liubo817/Diplomna-Rabota/Mechanical details/SmallBox.stl

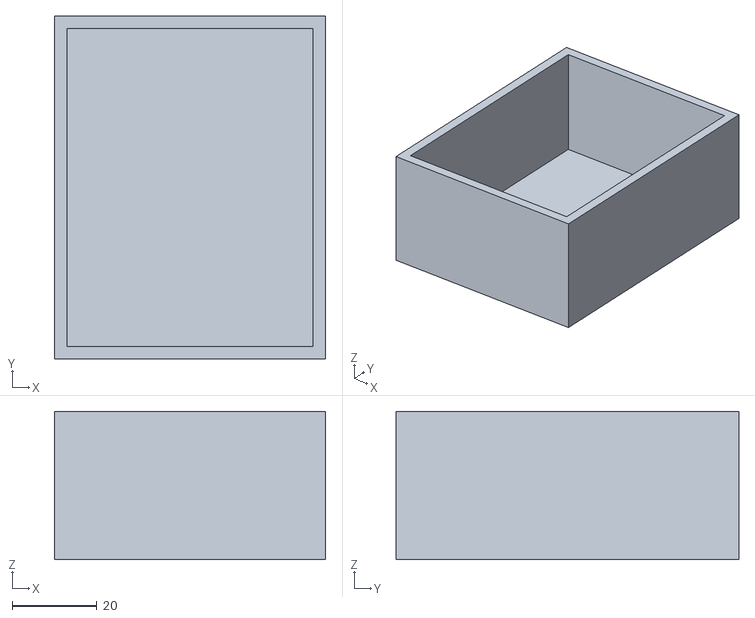
[picture p17: CAD file, 2024-02-20]
Mechanical details/SmallBox.stl
64.0 x 81.0 x 35.0
