liubo817/Diplomna-Rabota/Hardware/Libraries and 3D models/3p_con/connector_3p v1.step

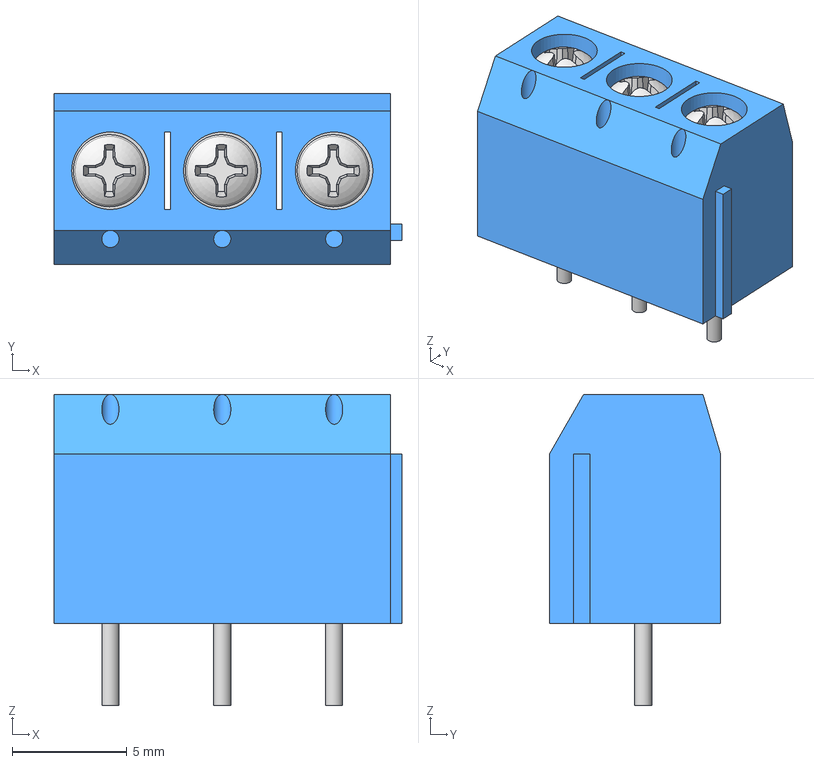
[picture p18: CAD file, 2024-01-03, an earlier design]
Hardware/Libraries and 3D models/3p_con/connector_3p v1.step
15.2 x 7.48 x 13.6 mm
