liubo817/Diplomna-Rabota/Hardware/Boards/FullBoard_V2/FullBoard.kicad_sch

## KiCad design Hardware/Boards/FullBoard_V2/FullBoard.kicad_sch (2024-01-07)

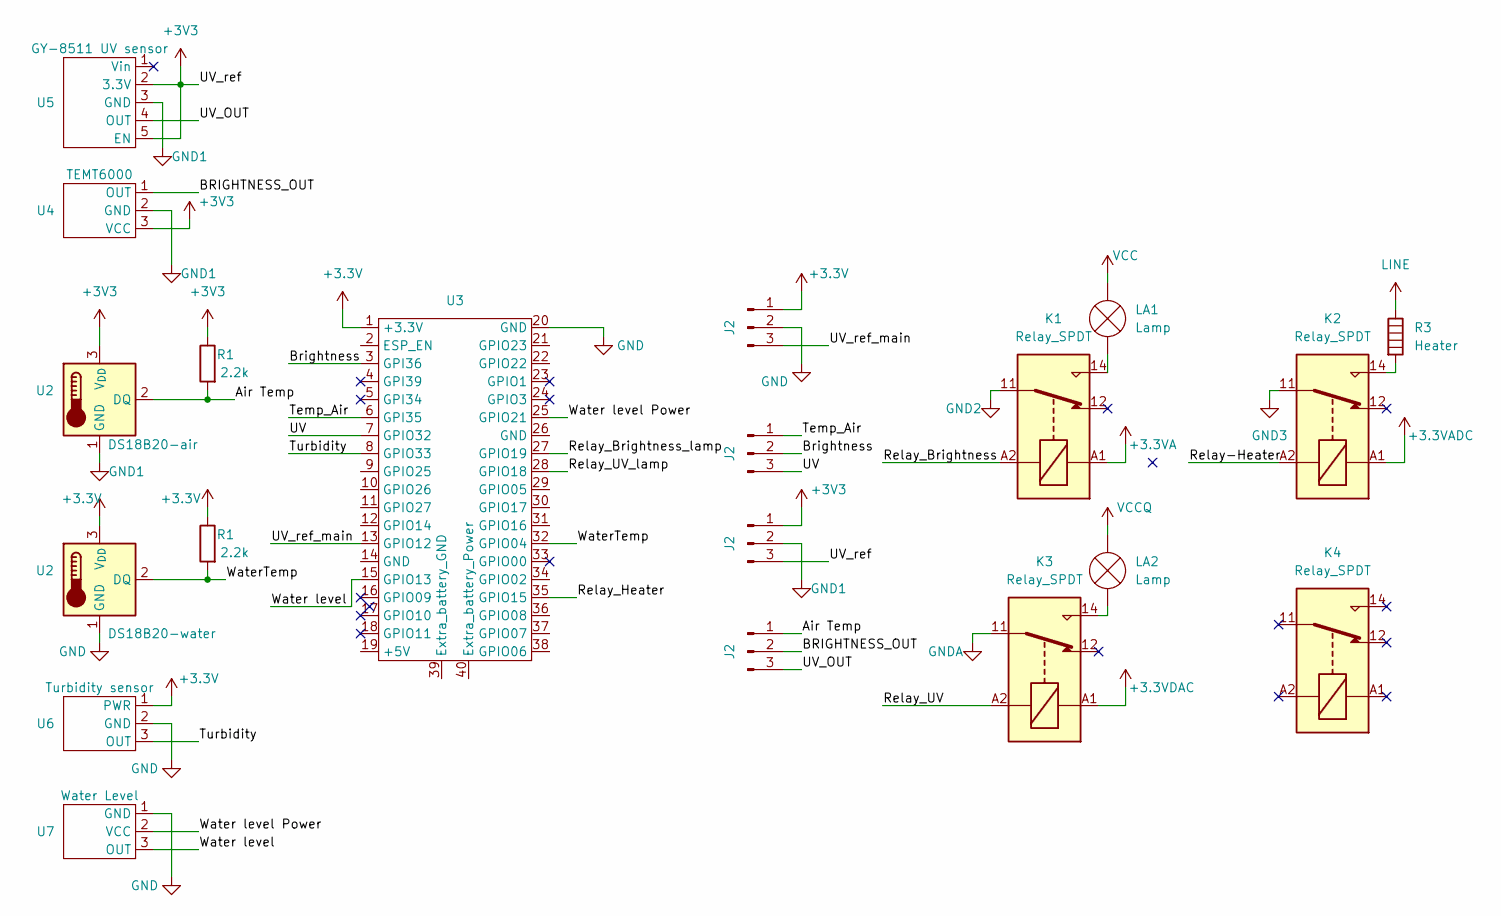
[picture p27: schematic FullBoard.kicad_sch]

Parts:
J2: Conn_01x03_Pin; connector_3p
K1, K2, K3: Relay_SPDT; Relay
K4: Relay_SPDT
LA1, LA2: Lamp
R1: 2.2k; R_Axial_DIN0204_L3.6mm_D1.6mm_P7.62mm_Horizontal
R3: Heater
U2: DS18B20-water; DS18B20_3dmodel
U3: MODULE_ESP32-DEVKITC
U4: TEMT6000; 3pin_holes
U5: GY-8511 UV sensor; 5pin_holes
U6: Turbidity sensor; 3pin_holes
U7: Water Level; 3pin_holes

Connections:
+3.3V: J2.1, R1.1, U2.3 (V_{DD}), U3.1 (+3.3V), U6.1 (PWR)
+3.3VA: K1.A1
+3.3VADC: K2.A1
+3.3VDAC: K3.A1
+3V3: J2.1, J2.3, R1.1, U2.3 (V_{DD}), U4.3 (VCC), U5.2 (3.3V), U5.5 (EN)
Air Temp: J2.1, R1.2, U2.2 (DQ)
BRIGHTNESS_OUT: J2.2, U4.1 (OUT)
Brightness: J2.2, U3.3 (GPI36)
GND: J2.2, U2.1 (GND), U3.20 (GND), U6.2 (GND), U7.1 (GND)
GND1: J2.2, U2.1 (GND), U4.2 (GND), U5.3 (GND)
GND2: K1.11
GND3: K2.11
GNDA: K3.11
LINE: R3.1
unnamed: K1.14, LA1.1 (-)
unnamed: K2.14, R3.2
unnamed: K3.14, LA2.1 (-)
Relay-Heater: K2.A2
Relay_Brightness: K1.A2
Relay_Brightness_lamp: U3.27 (GPIO19)
Relay_Heater: U3.35 (GPIO15)
Relay_UV: K3.A2
Relay_UV_lamp: U3.28 (GPIO18)
Temp_Air: J2.1, U3.6 (GPI35)
Turbidity: U3.8 (GPIO33), U6.3 (OUT)
UV: J2.3, U3.7 (GPIO32)
UV_OUT: J2.3, U5.4 (OUT)
UV_ref_main: J2.3, U3.13 (GPIO12)
VCC: LA1.2 (+)
VCCQ: LA2.2 (+)
Water level: U3.15 (GPIO13), U7.3 (OUT)
Water level Power: U3.25 (GPIO21), U7.2 (VCC)
WaterTemp: R1.2, U2.2 (DQ), U3.32 (GPIO04)
