liubo817/Diplomna-Rabota/Software/WaterTemp/src/main.cpp

#include <Arduino.h>
#include <OneWire.h>
#include <DallasTemperature.h>

#define ONE_WIRE_BUS 4

OneWire oneWire(ONE_WIRE_BUS);	
DallasTemperature sensors(&oneWire);

void setup(void)
{
  sensors.begin();	// Start up the library
  Serial.begin(9600);
}

void loop(void)
{ 
  sensors.requestTemperatures(); 
  Serial.print("Temperature: ");
  Serial.print(sensors.getTempCByIndex(0));
  Serial.print("C");
  Serial.println();
  delay(500);
}
